przemyslaw-turek/gm/ESP8266/esp.png

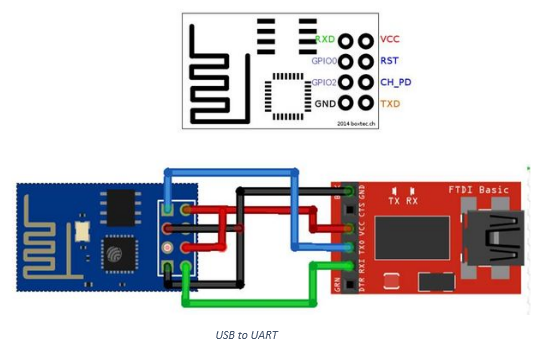
ESP8266/esp.png
