przemyslaw-turek/gm/Extra files/ha1.png

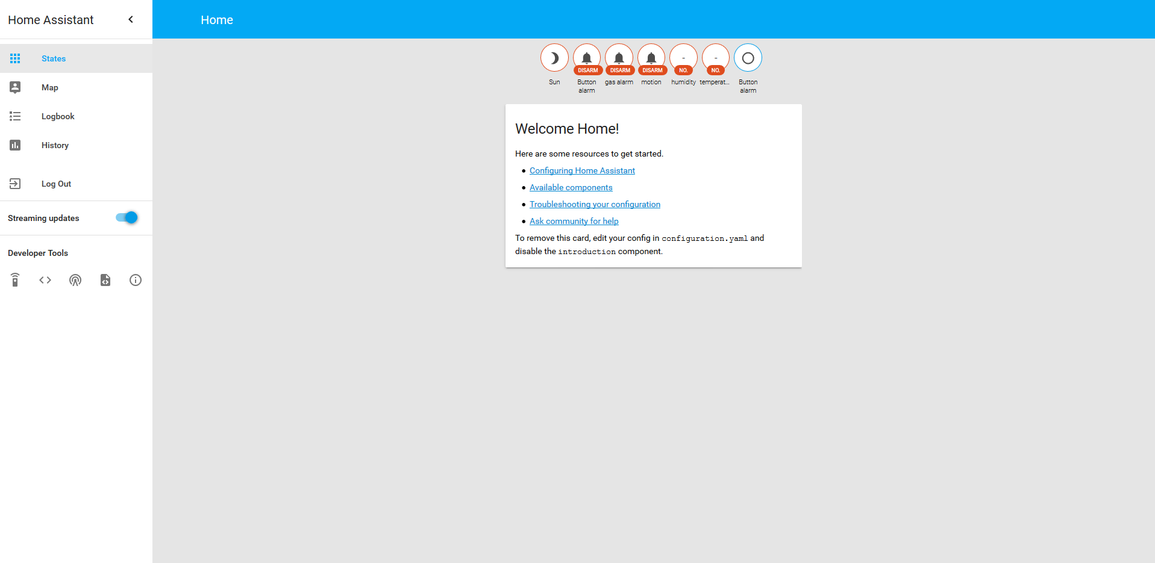
Extra files/ha1.png
