przemyslaw-turek/gm/Extra files/ha2.png

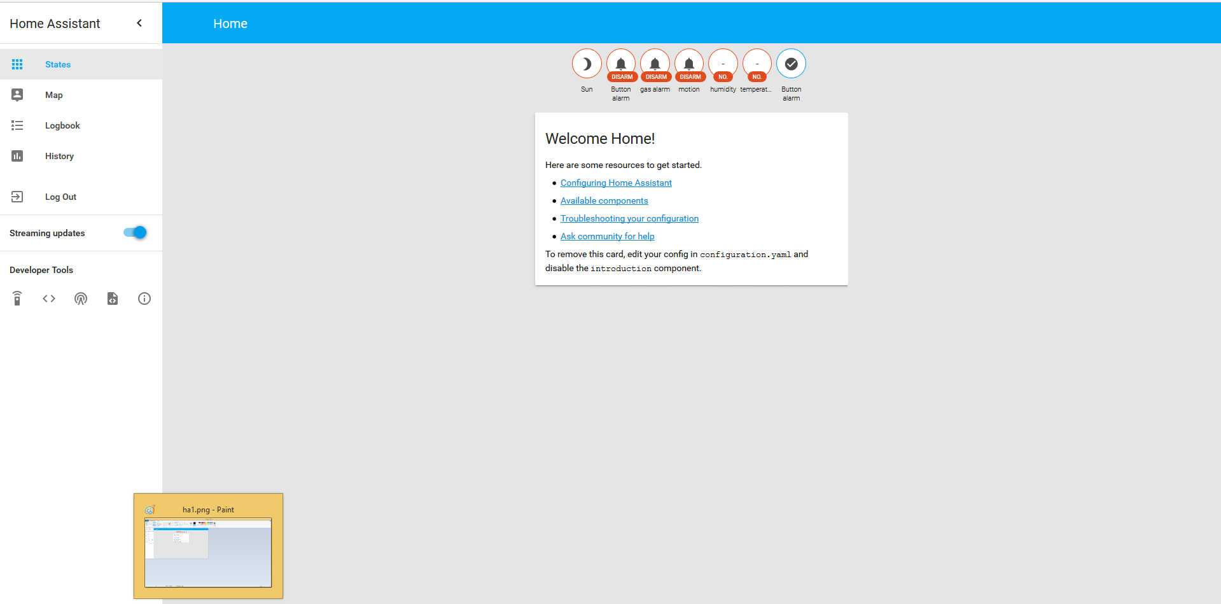
Extra files/ha2.png
