przemyslaw-turek/gm/Extra files/ha3.png

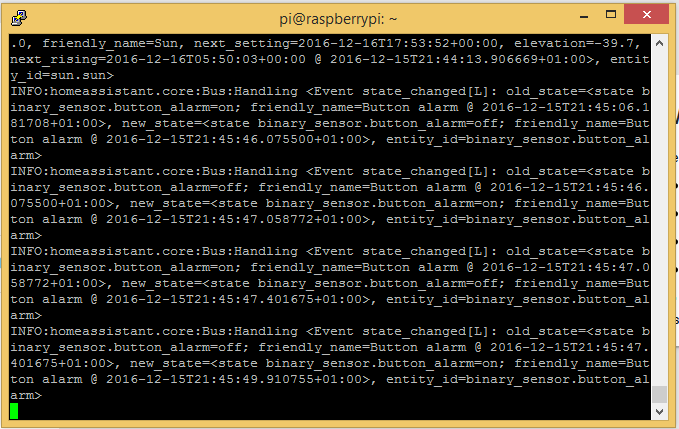
Extra files/ha3.png
