przemyslaw-turek/gm/hardware/sensors/motion/esp.jpg

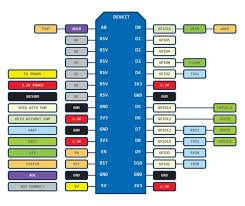
hardware/sensors/motion/esp.jpg
