przemyslaw-turek/gm/RaspberryPi/software/HomeAssistant/nano4.png

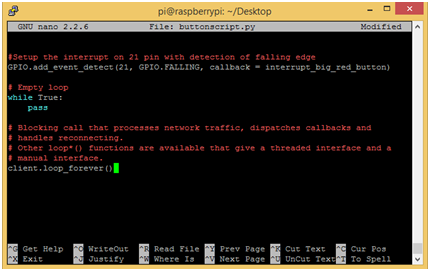
RaspberryPi/software/HomeAssistant/nano4.png
